phrxmd/touchlesstool/stl/touchlesstool-6mm-endcap-noscrew.stl

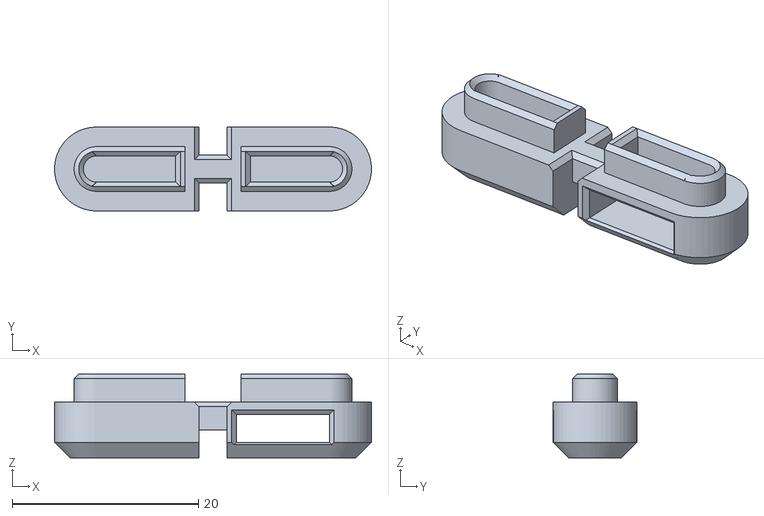
[picture p23: CAD file, 2020-04-06]
stl/touchlesstool-6mm-endcap-noscrew.stl
34.0 x 9.00 x 9.00
