phrxmd/touchlesstool/stl/touchlesstool-6mm-NOSCREW-sleeve.stl

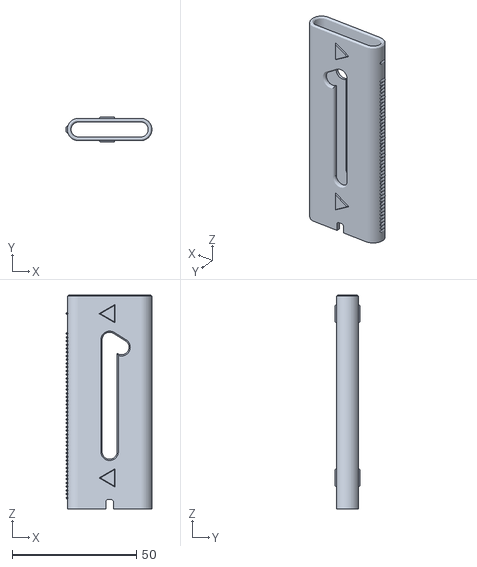
[picture p24: CAD file, 2020-04-06]
stl/touchlesstool-6mm-NOSCREW-sleeve.stl
34.5 x 10.0 x 86.0
