phrxmd/touchlesstool/stl/touchlesstool-6mm-NOSCREW-bolts-robust.stl

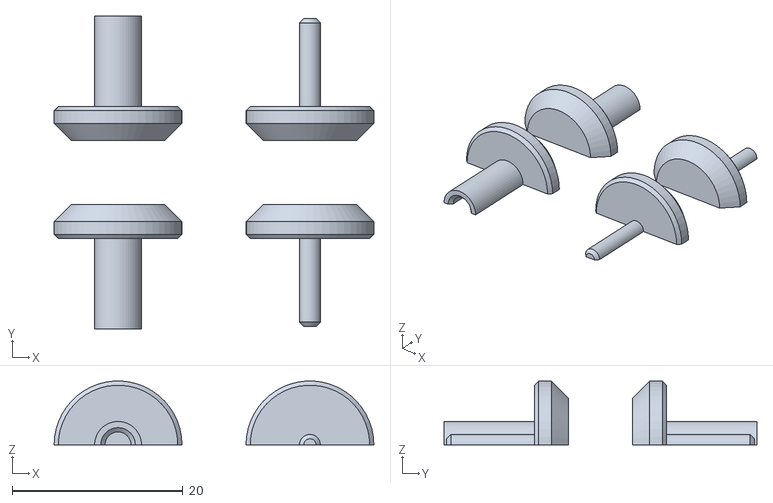
[picture p25: CAD file, 2020-04-06]
stl/touchlesstool-6mm-NOSCREW-bolts-robust.stl
37.5 x 36.7 x 7.49
